Lightningyc/MPPT_Buck-Boost/program/buck_boost/system/move_filter.h

//
// Created by 黄 on 2024/5/25.
//

#ifndef _MOVE_FILTER_H
#define _MOVE_FILTER_H


#include "main.h"

extern float V_advalue_moveAverageFilter(uint32_t input_data);

extern float A_advalue_moveAverageFilter(uint32_t input_data);

#endif
